v9938/MSX_GamingLED/img/img002.jpg

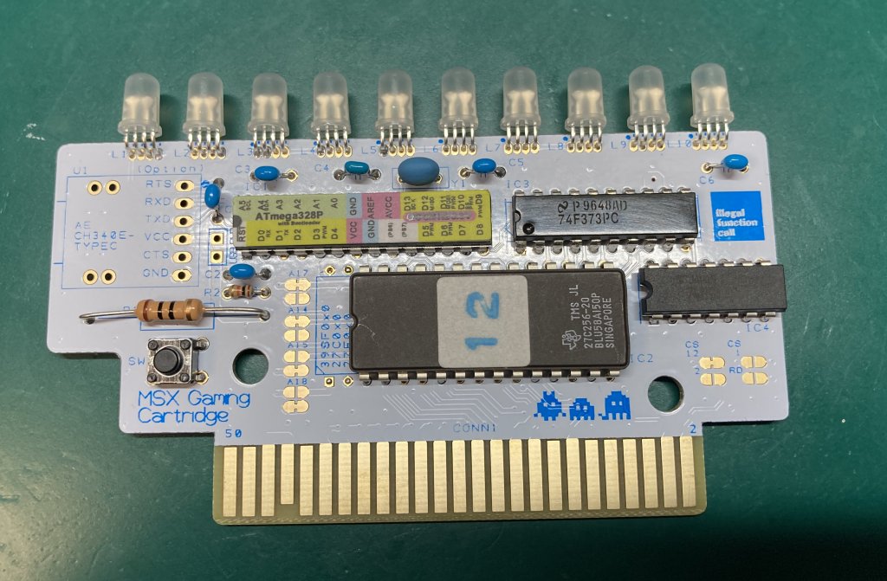
img/img002.jpg
