v9938/MSX_GamingLED/img/scope_22.bmp

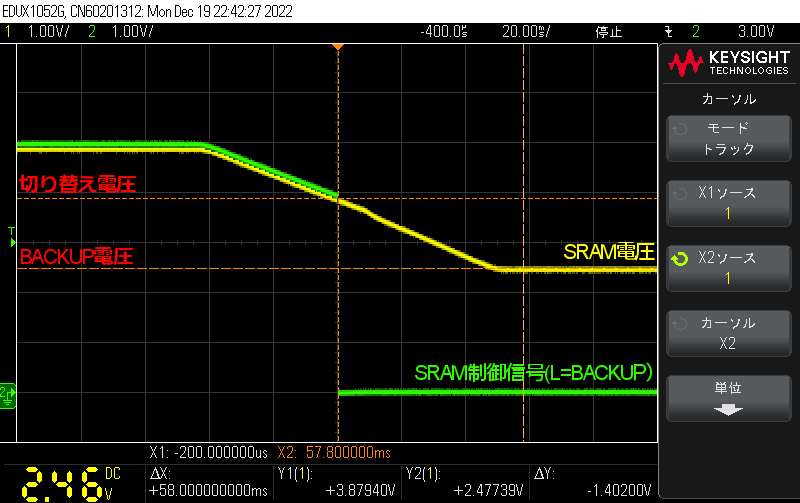
img/scope_22.bmp
