v9938/MSX_GamingLED/PCB/BOTTOM.png

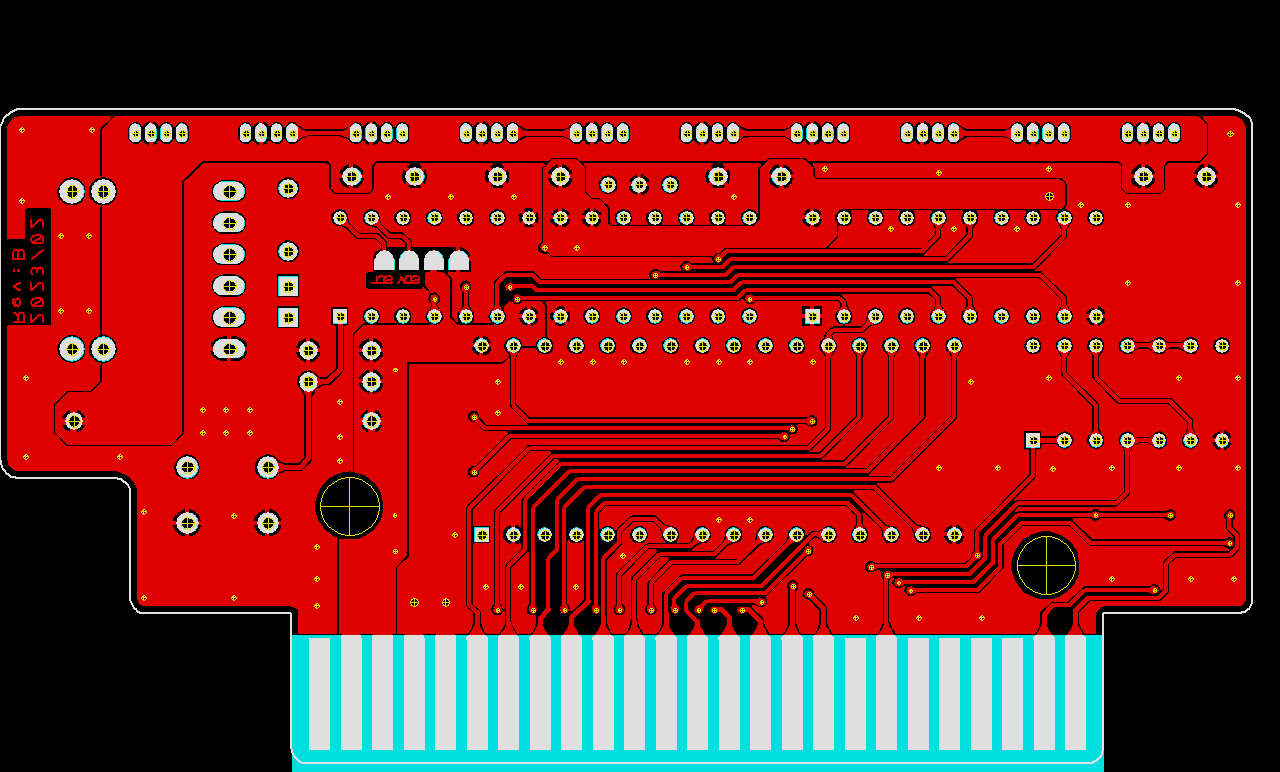
PCB/BOTTOM.png
