v9938/MSX_GamingLED/PCB/MSX_GamingLED Schematic.png

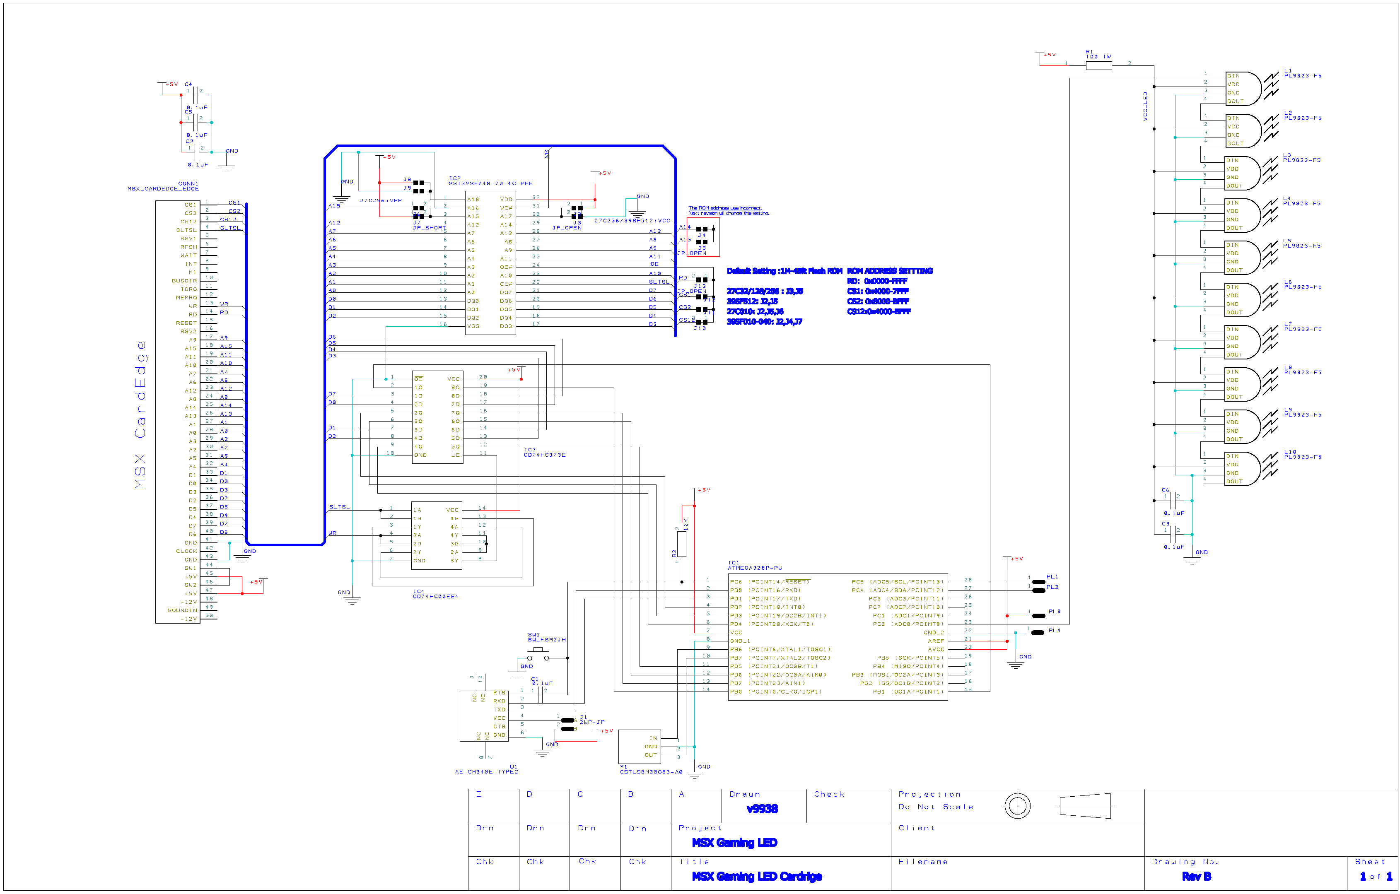
PCB/MSX_GamingLED Schematic.png
