v9938/MSX_GamingLED/PCB/TOP.png

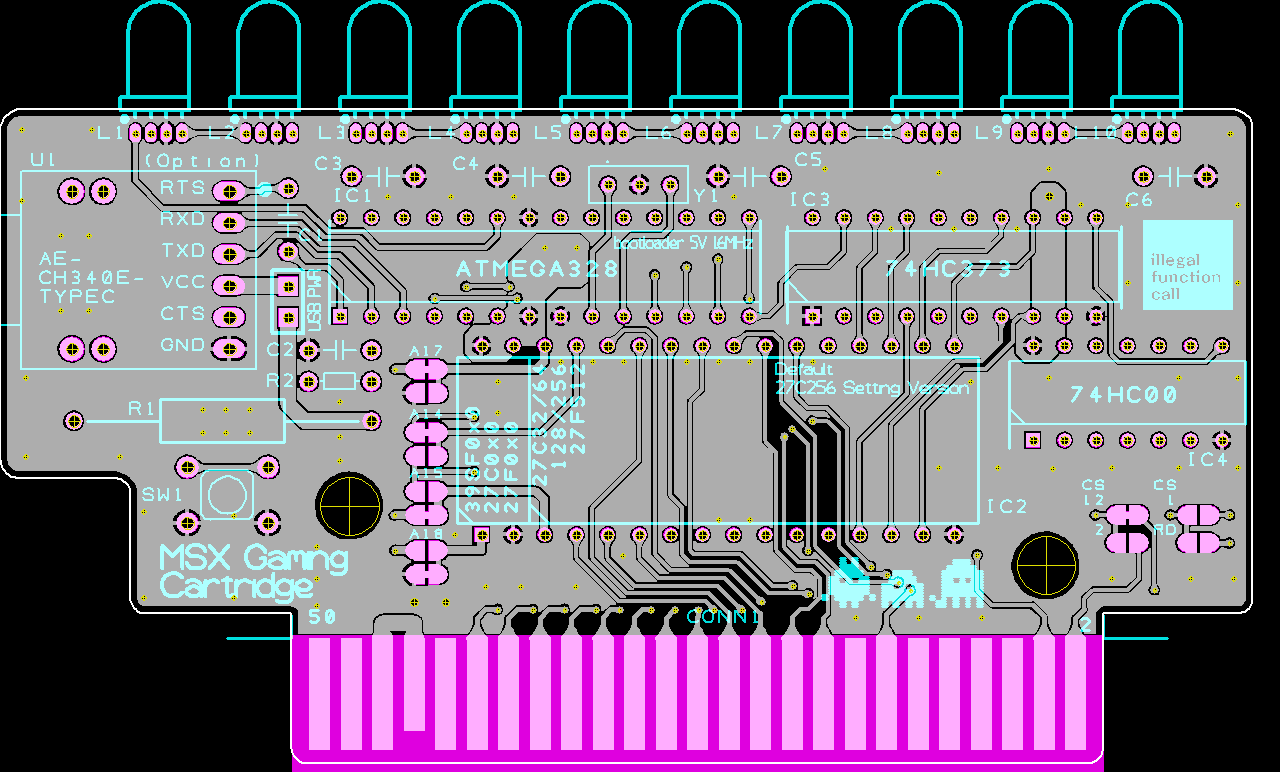
PCB/TOP.png
