v9938/MSX_GamingLED/SampleApplication/BASIC/TESTRGB.BAS

100 CLS:LOCATE0,10:PRINT"MSX Gaming LED Cartridge":PRINT"RGB mode sample V1.0":PRINT"Copyrigth 2023/02 @v9938
110 _LED_OFF:_LED_POS(0):_LEDC_HUE(0):_LEDC_SAT(0):_LEDC_VAL(0):_LED_PT(0)
120 _LEDPT_HUE(240):_LEDPT_SAT(0):_LEDPT_VAL(100):_LED_DRAW:_LEDC_RGB(0,0,127):_LED_DRAW
130 _LED_PT(4)
140 FORI=0TO9:_LEDPT_RGB(I,127,0,0):_LED_DRAW:FORX=0TO99:NEXT:_LEDPT_RGB(I,0,0,10):NEXT
150 GOTO 140
